angelmon091/Line-Followers-1.0/Imagenes Turbinas/3.PNG

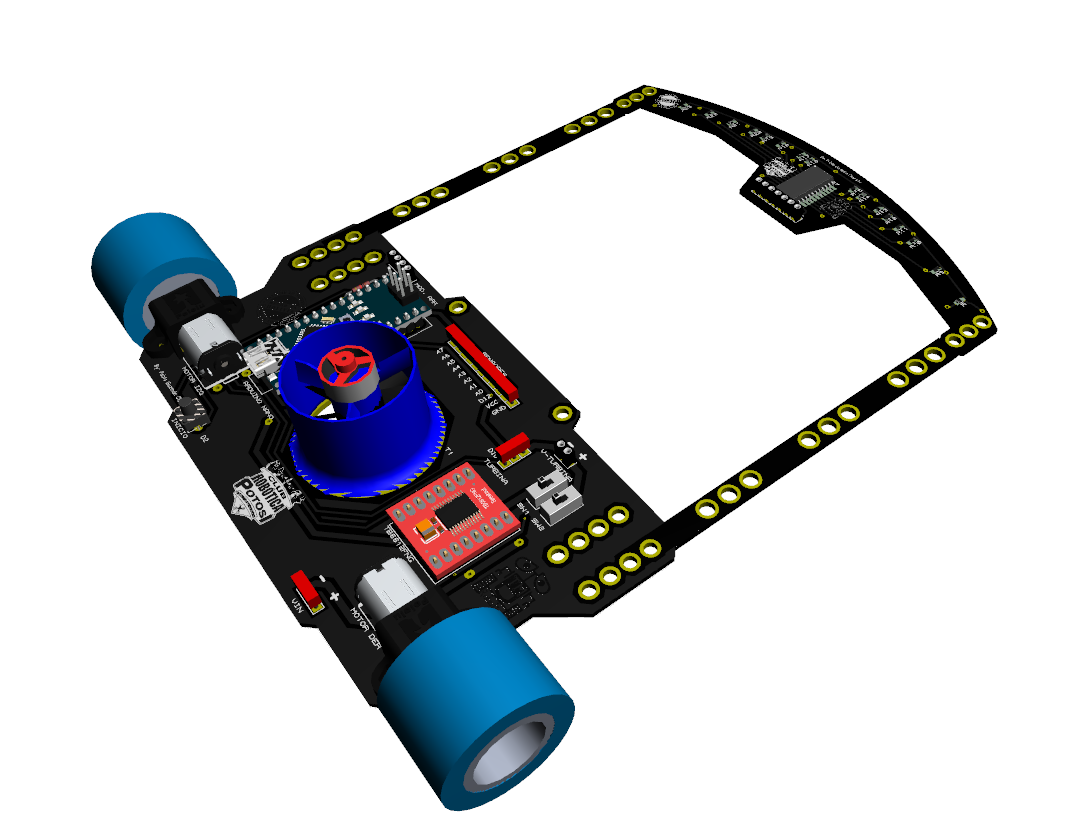
Imagenes Turbinas/3.PNG
