angelmon091/Line-Followers-1.0/Imagenes Turbinas/4.PNG

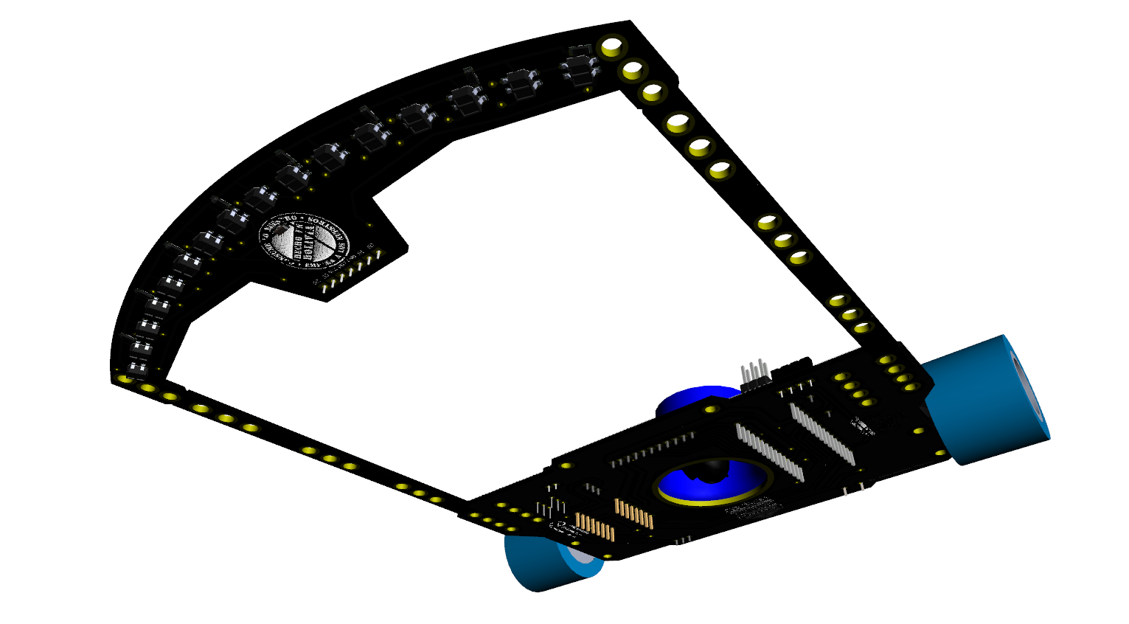
Imagenes Turbinas/4.PNG
