angelmon091/Line-Followers-1.0/Imagenes Turbinas/5.PNG

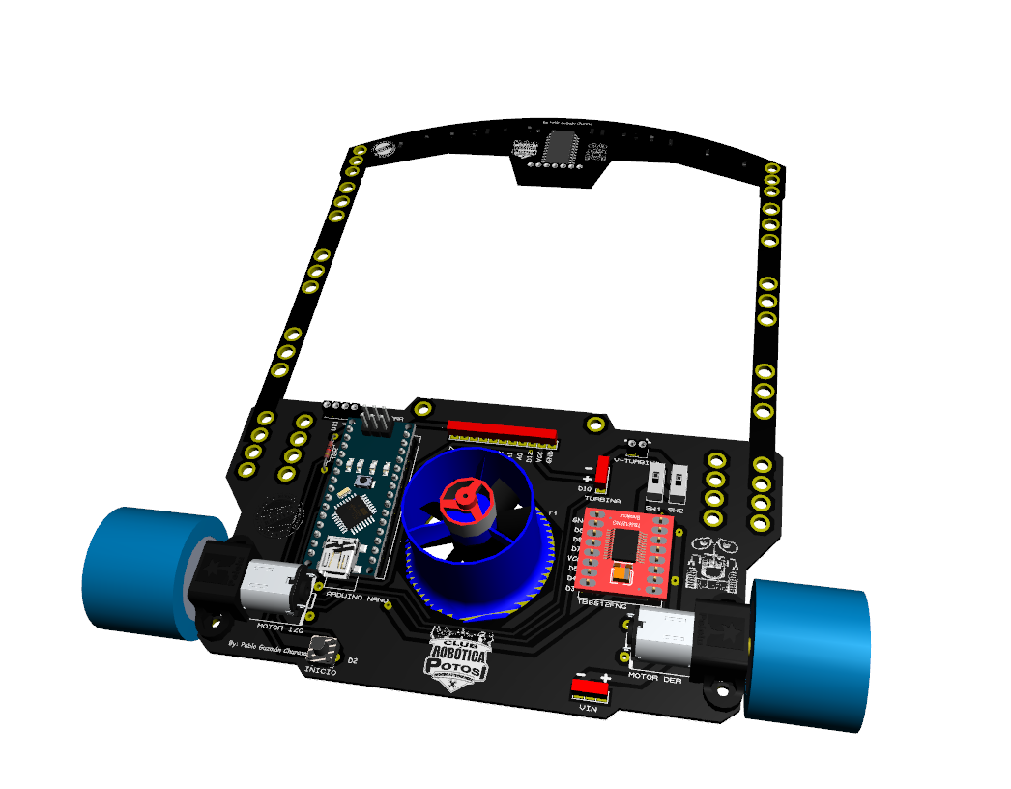
Imagenes Turbinas/5.PNG
